tigerbot-team/tigerbot/nebula-captures/run-7-fail-yellow-green/nebula-image-3.jpg

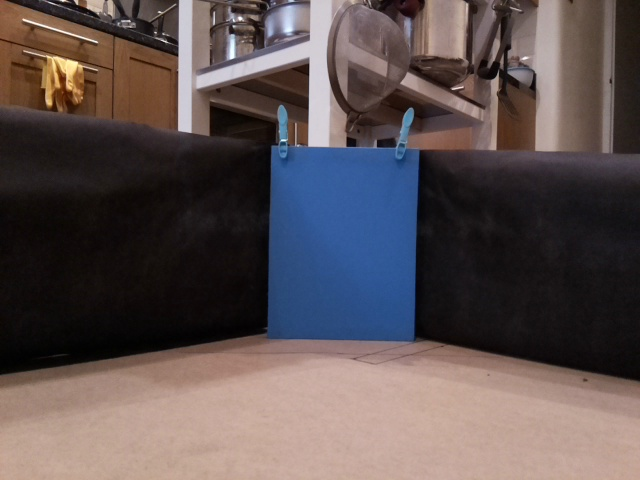
nebula-captures/run-7-fail-yellow-green/nebula-image-3.jpg
