tigerbot-team/tigerbot/camera-experiments/new-pics/further.jpg

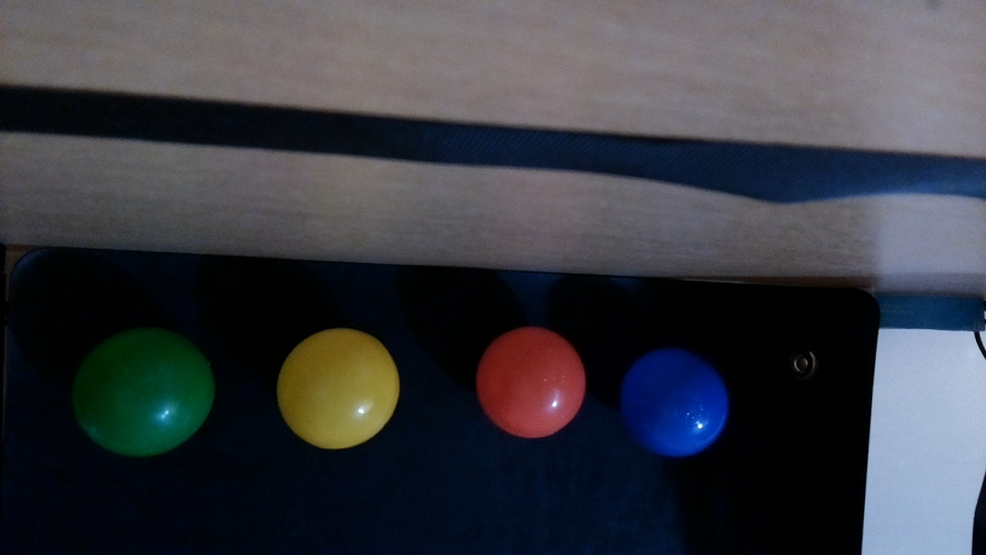
camera-experiments/new-pics/further.jpg
