tigerbot-team/tigerbot/camera-experiments/new-pics/pic1.jpg

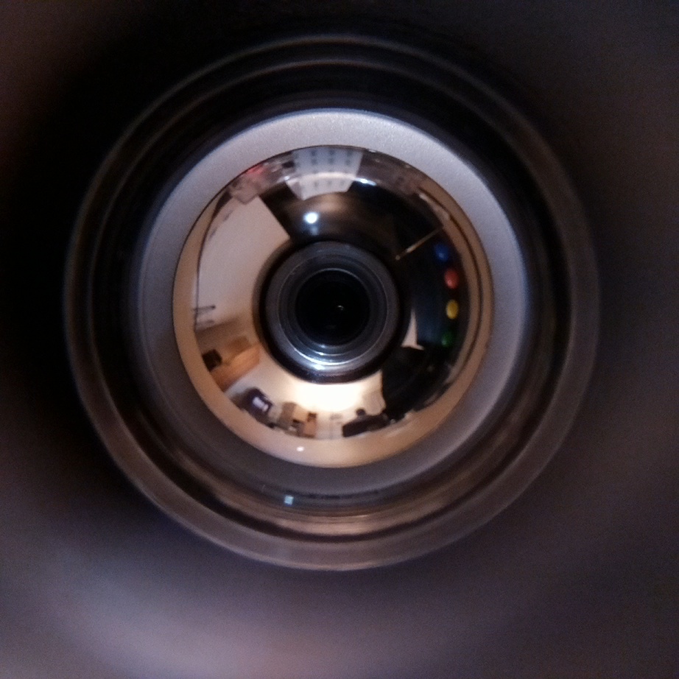
camera-experiments/new-pics/pic1.jpg
