tigerbot-team/tigerbot/python-controller/simpleRobot.py

import time

import gobject
import serial

from joy import Joystick


class Motor:
    def __init__(self):
        self.serialportname = "/dev/ttyAMA0"
        self.serialportspeed = 115200
        self.motorone = 0
        self.motortwo = 0
        self.update_motor()

    def one(self, power):
        self.motorone = power
        self.update_motor()

    def two(self, power):
        self.motortwo = power
        self.update_motor()

    def update_motor(self):
        with serial.Serial(self.serialportname, self.serialportspeed, timeout=1) as ser:
            command = "+sa %s %s %s %s\n" % (self.motorone,
                                           self.motortwo,
                                           self.motorone,
                                           self.motortwo)
            print "sending: %s" % command
            ser.write(command)

    def stop(self):
        self.motorone = 0
        self.motortwo = 0
        self.update_motor()


class Robot:
    def __init__(self):
        # Setup
        self.x_axis = 0.0
        self.y_axis = 0.0
        self.max_power = 1.0
        self.disable_motor = True
        self.motor = Motor()

    def mixer(self, in_yaw, in_throttle):
        left = in_throttle + in_yaw
        right = in_throttle - in_yaw
        scale_left = abs(left / 125.0)
        scale_right = abs(right / 125.0)
        scale_max = max(scale_left, scale_right)
        scale_max = max(1, scale_max)
        out_left = int(self.constrain(left / scale_max, -125, 125))
        out_right = int(self.constrain(right / scale_max, -125, 125))
        results = [out_right, out_left]
        return results

    @staticmethod
    def constrain(val, min_val, max_val):
        return min(max_val, max(min_val, val))

    def update_motor(self):
        mixer_results = self.mixer(self.x_axis, self.y_axis)
        # print (mixer_results)
        power_left = int((mixer_results[0] / 125.0) * 100)
        power_right = int((mixer_results[1] / 125.0) * 100)
        print("left: " + str(power_left) + " right: " + str(power_right))

        if not self.disable_motor:
            self.motor.one((-power_right * self.max_power))
            self.motor.two((power_left * self.max_power))

    def axis_handler(self, signal, number, value, init):
        # Axis 0 = left stick horizontal.  -ve = left
        # Axis 1 = left stick vertical.    -ve = up
        # Axis 5 = right stick vertical.   -ve = up
        # Axis 2 = right stick horizontal. -ve left
        if number == 5:
            if value > 130:
                print("Backwards")
            elif value < 125:
                print("Forward")
            self.y_axis = value
            if self.y_axis > 130:
                self.y_axis = -(self.y_axis - 130)
            elif self.y_axis < 125:
                self.y_axis = ((-self.y_axis) + 125)
            else:
                self.y_axis = 0.0
        elif number == 2:
            if value > 130:
                print("Right")
            elif value < 125:
                print("Left")
            self.x_axis = value
            if self.x_axis > 130:
                self.x_axis = (self.x_axis - 130)
            elif self.x_axis < 125:
                self.x_axis = -((-self.x_axis) + 125)
            else:
                self.x_axis = 0.0
            print("X: " + str(self.x_axis))
        self.update_motor()

    def run(self):
        try:
            j = Joystick(0)
            j.connect('axis', self.axis_handler)
            loop = gobject.MainLoop()
            context = loop.get_context()
            while True:
                if context.pending():
                    context.iteration(True)
                else:
                    time.sleep(0.01)
        except Exception, e:
            print(e)
            print("stop")
            self.motor.stop()
        print("bye")


if __name__ == "__main__":
    robot = Robot()
    robot.run()
